koreever66/kineshoot-initial-debug-v1/photos/breadboard_original.jpg

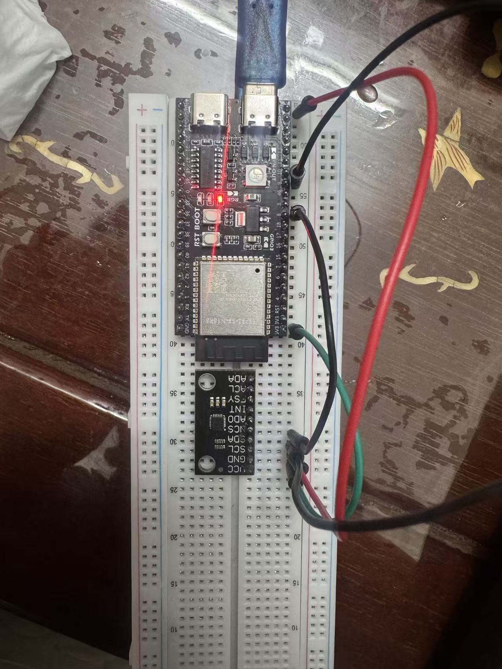
photos/breadboard_original.jpg
