koreever66/kineshoot-initial-debug-v1/photos/H2/2026-09-18_tps61088_back.jpg

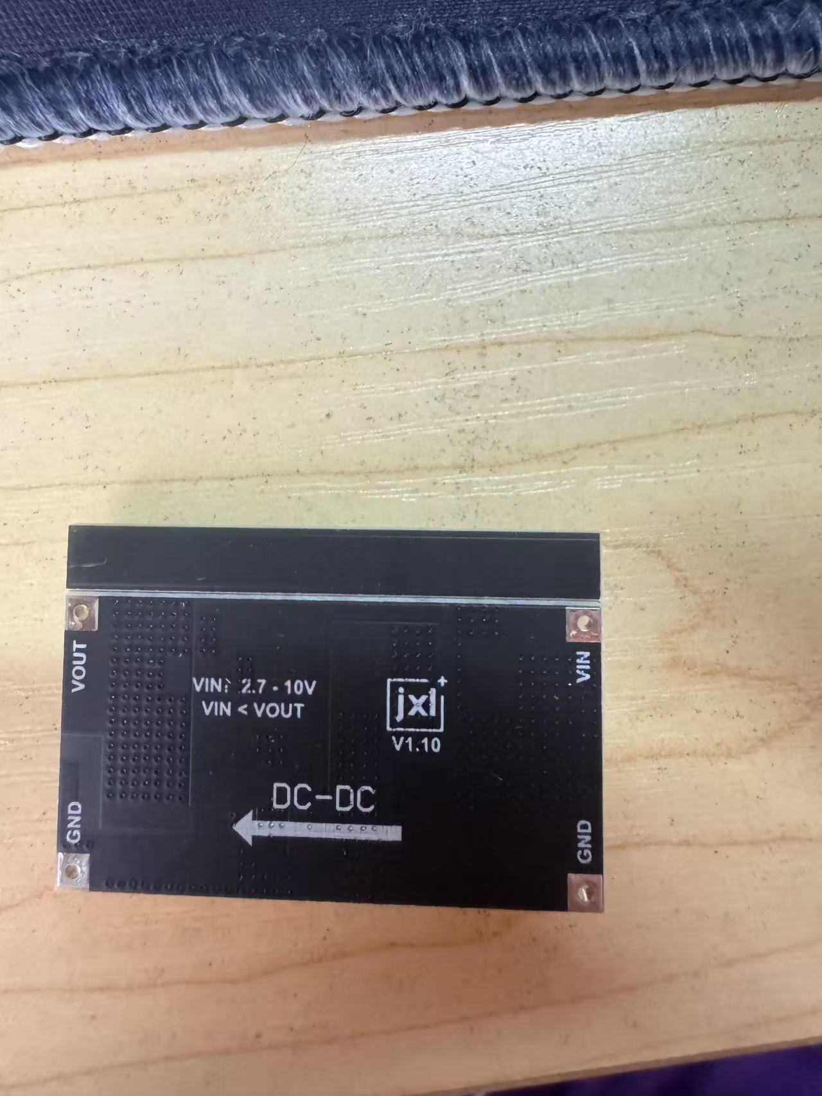
photos/H2/2026-09-18_tps61088_back.jpg
