koreever66/kineshoot-initial-debug-v1/plots/imu_20260913_193817_plot.png

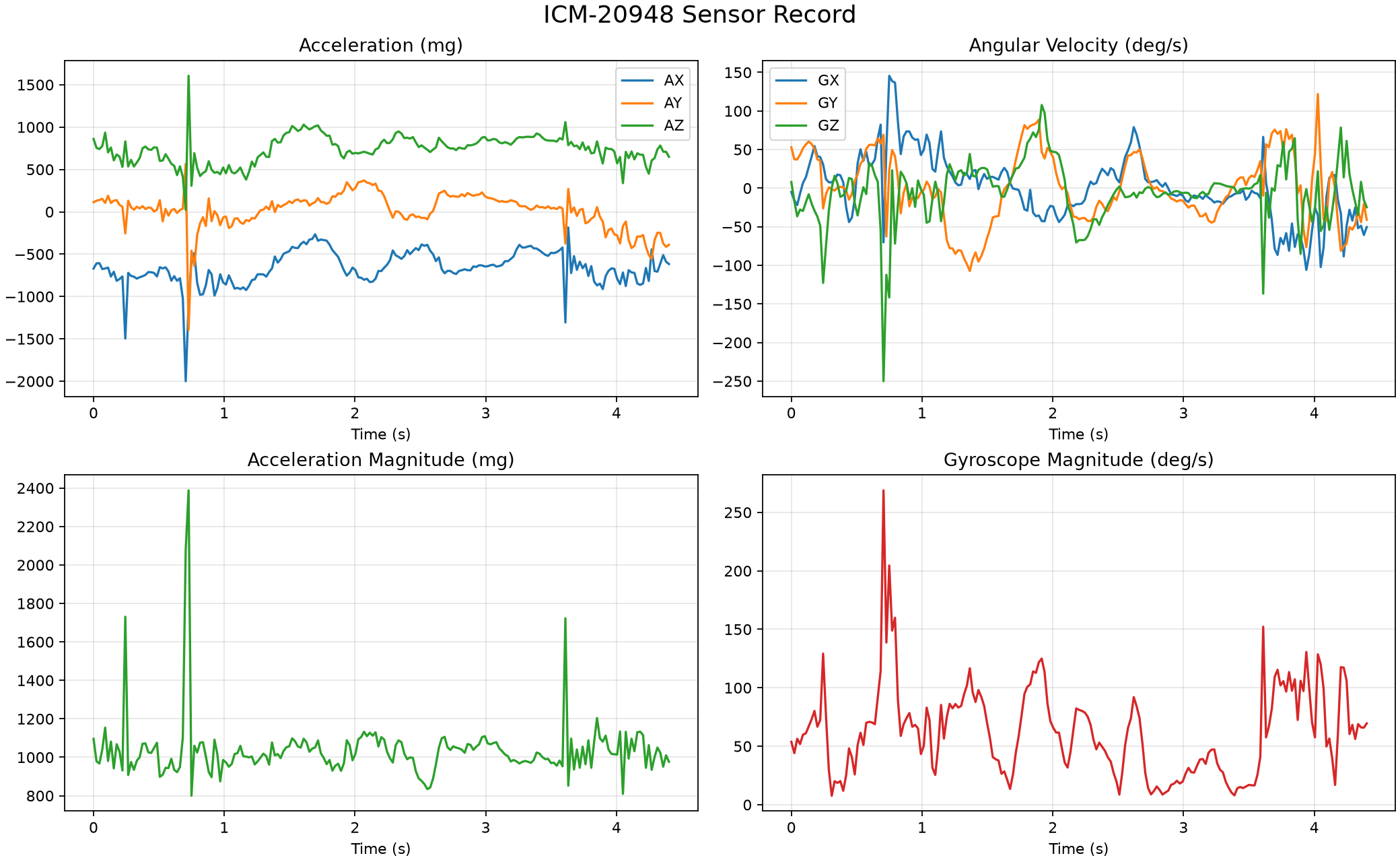
plots/imu_20260913_193817_plot.png
