koreever66/kineshoot-initial-debug-v1/plots/imu_20260913_194905_plot.png

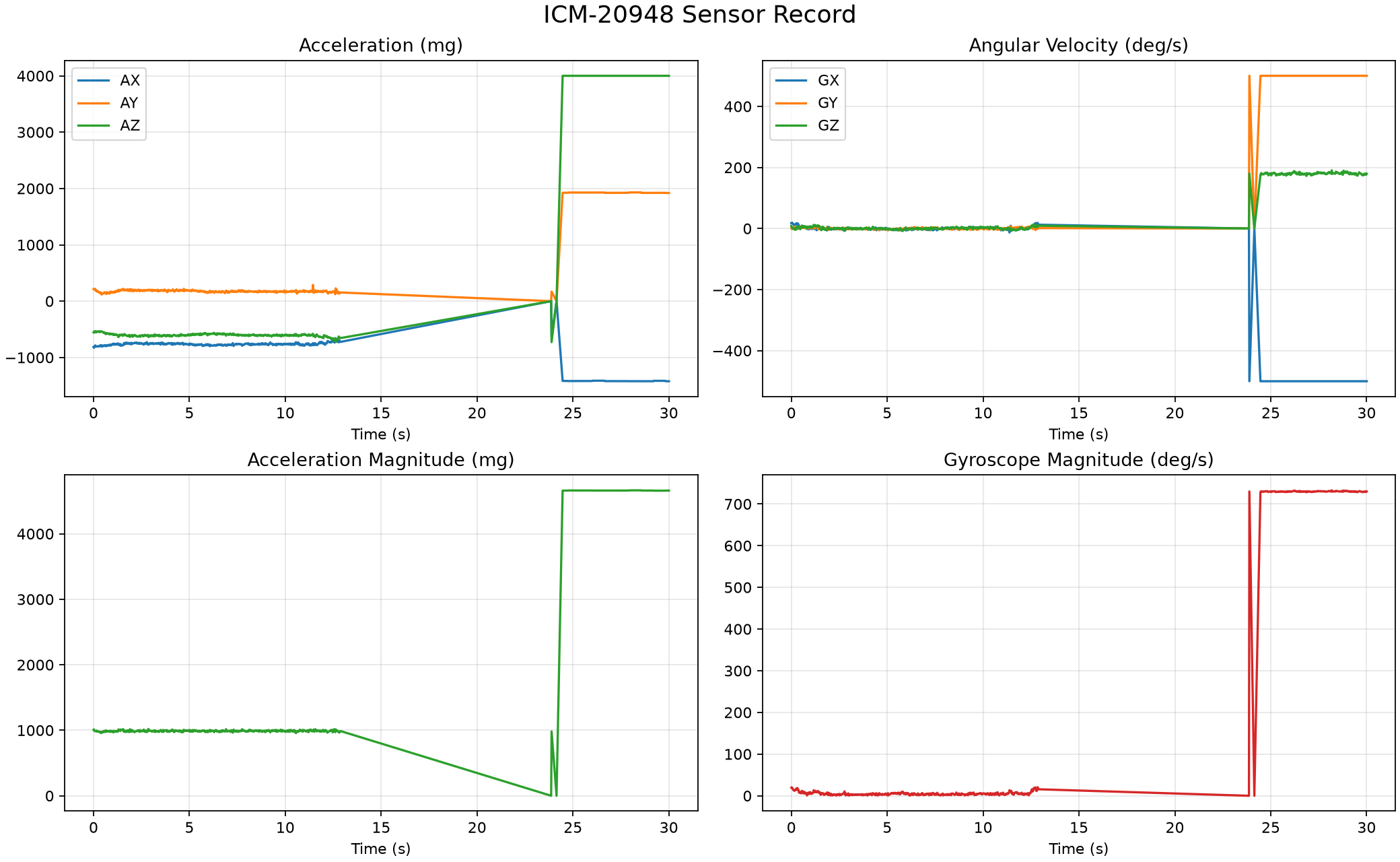
plots/imu_20260913_194905_plot.png
