koreever66/kineshoot-initial-debug-v1/docs/hardware/design/node2_preassembly_v1.png

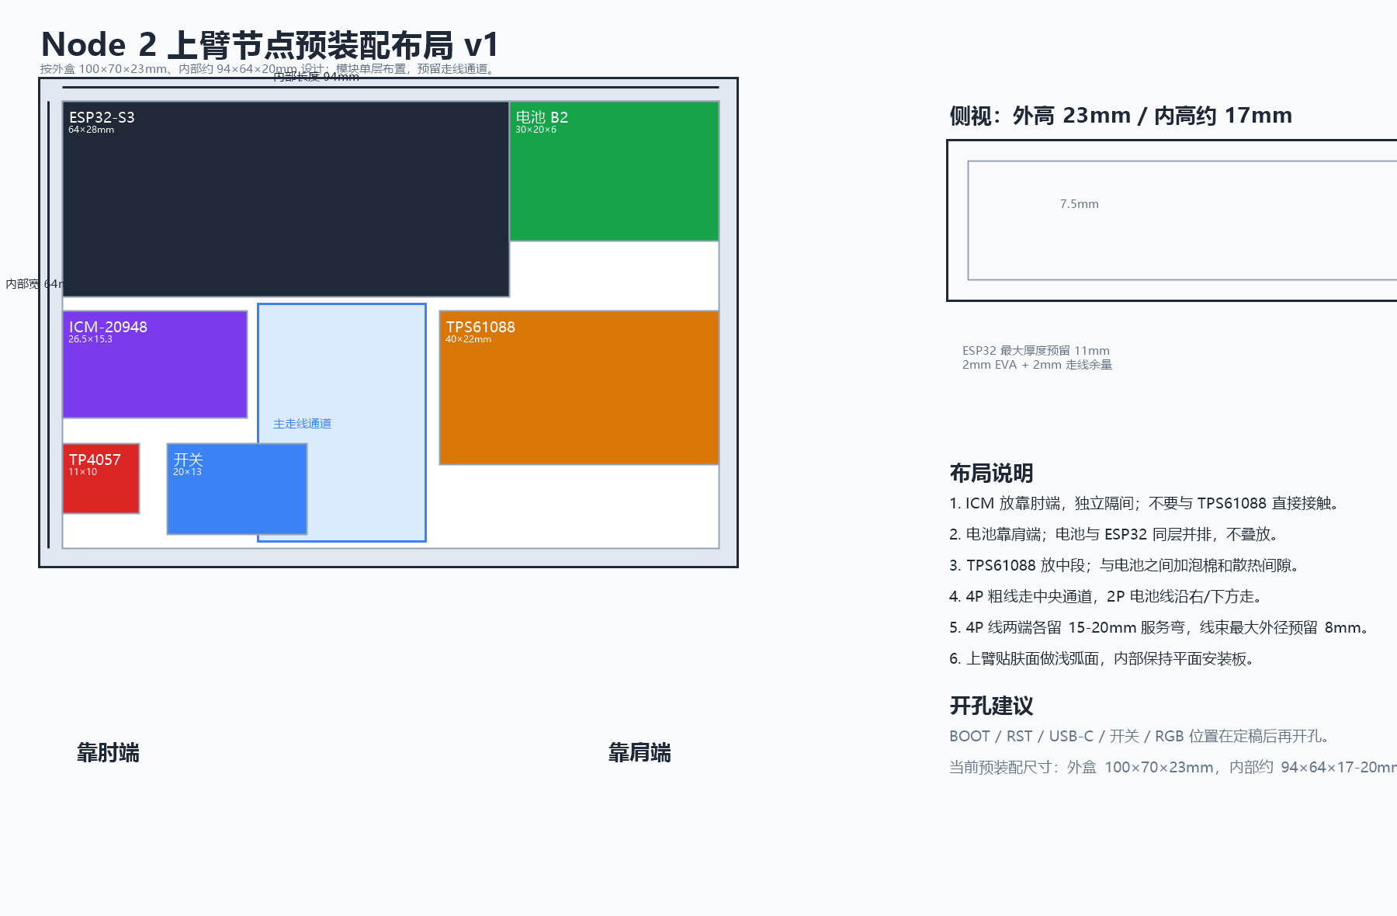
docs/hardware/design/node2_preassembly_v1.png
